Kacman62/Moonbeam-Synthesizer/CodeFolder/images.cpp

#include "images.h"

const unsigned char PKI_Logo_BW[] = {
    // 'PKIndustries_LowRes_BW', 128x64px
    0x00, 0x00, 0x00, 0x00, 0x00, 0x00, 0x00, 0x00, 0x00, 0x00, 0x00, 0x00, 0x00, 0x00, 0x00, 0x01,
    0x00, 0x00, 0x00, 0x00, 0x00, 0x00, 0x00, 0x00, 0x00, 0x00, 0x00, 0x00, 0x00, 0x00, 0x00, 0x01,
    0x00, 0x00, 0x00, 0x00, 0x00, 0x00, 0x00, 0x00, 0x00, 0x00, 0x00, 0x00, 0x00, 0x00, 0x00, 0x01,
    0x00, 0x00, 0x00, 0x00, 0x00, 0x00, 0x00, 0x00, 0x00, 0x00, 0x00, 0x00, 0x00, 0x00, 0x00, 0x01,
    0x00, 0x00, 0x00, 0x00, 0x00, 0x00, 0x00, 0x00, 0x00, 0x00, 0x00, 0x00, 0x00, 0x00, 0x00, 0x01,
    0x00, 0x00, 0x00, 0x00, 0x00, 0x00, 0x00, 0x00, 0x00, 0x00, 0x00, 0x00, 0x00, 0x00, 0x00, 0x01,
    0x00, 0x00, 0x00, 0x00, 0x00, 0x00, 0x00, 0x00, 0x00, 0x00, 0x00, 0x00, 0x20, 0x00, 0x00, 0x01,
    0x00, 0x00, 0x00, 0x00, 0x00, 0x00, 0x00, 0x00, 0x00, 0x00, 0x00, 0x00, 0x20, 0x00, 0x00, 0x01,
    0x00, 0x00, 0x00, 0x00, 0x00, 0x00, 0x00, 0x00, 0x00, 0x00, 0x00, 0x00, 0x20, 0x00, 0x00, 0x01,
    0x00, 0x00, 0x00, 0x00, 0x00, 0x00, 0x00, 0x00, 0x00, 0x00, 0x00, 0x00, 0x20, 0x00, 0x00, 0x01,
    0x00, 0x00, 0x00, 0x00, 0x00, 0x00, 0x00, 0x00, 0x00, 0x00, 0x00, 0x00, 0x20, 0x00, 0x00, 0x01,
    0x00, 0x00, 0x00, 0x00, 0x00, 0x00, 0x00, 0x00, 0x00, 0x00, 0x00, 0x00, 0x20, 0x00, 0x00, 0x01,
    0x00, 0x00, 0x00, 0x00, 0x00, 0x00, 0x00, 0x00, 0x00, 0x00, 0x00, 0x00, 0x20, 0x00, 0x00, 0x01,
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

const unsigned char *notes[7] = {
    A, B, C, D, E, F, G};

// 'MoonBeamSynthExport', 8x8px
const unsigned char sharp[] = {
    0x00, 0x28, 0x7c, 0x28, 0x7c, 0x28, 0x00, 0x00};
// 'MoonBeamSynthExport', 8x8px
const unsigned char flat[] = {
    0x00, 0x40, 0x40, 0x70, 0x50, 0x70, 0x00, 0x00};

// 'MoonBeamSynthExport', 3x5px
const unsigned char one[] = {
    0x20, 0x20, 0x20, 0x20, 0x20};
// 'MoonBeamSynthExport', 3x5px
const unsigned char two[] = {
    0xc0, 0x20, 0x40, 0x80, 0xe0};
// 'MoonBeamSynthExport', 3x5px
const unsigned char three[] = {
    0xe0, 0x20, 0xe0, 0x20, 0xe0};
// 'MoonBeamSynthExport', 3x5px
const unsigned char four[] = {
    0xa0, 0xa0, 0xe0, 0x20, 0x20};
// 'MoonBeamSynthExport', 3x5px
const unsigned char five[] = {
    0xe0, 0x80, 0x40, 0x20, 0xc0};
// 'MoonBeamSynthExport', 3x5px
const unsigned char six[] = {
    0xe0, 0x80, 0xe0, 0xa0, 0xe0};
// 'MoonBeamSynthExport', 3x5px
const unsigned char seven[] = {
    0xe0, 0x20, 0x40, 0x40, 0x40};
// 'MoonBeamSynthExport', 3x5px
const unsigned char eight[] = {
    0xe0, 0xa0, 0xe0, 0xa0, 0xe0};
// 'MoonBeamSynthExport', 3x5px
const unsigned char nine[] = {
    0xe0, 0xa0, 0xe0, 0x20, 0xe0};
// 'MoonBeamSynthExport', 3x5px
const unsigned char zero[] = {
    0xe0, 0xa0, 0xa0, 0xa0, 0xe0};

// Array of all bitmaps for convenience. (Total bytes used to store images in PROGMEM = 160)

const unsigned char *numbers[10] = {
    zero, one, two, three, four, five, six, seven, eight, nine};

// 'MoonBeamSynthExport', 3x5px
const unsigned char plus[] = {
    0x00, 0x40, 0xe0, 0x40, 0x00};
// 'MoonBeamSynthExport', 3x5px
const unsigned char minus[] = {
    0x00, 0x00, 0xe0, 0x00, 0x00};
