Kacman62/Moonbeam-Synthesizer/CodeFolder/images.h

#ifndef IMAGES_H
#define IMAGES_H

extern const unsigned char PKI_Logo_BW[];

extern const unsigned char MoonBeamSynth[];

extern const unsigned char sinWave[];
extern const unsigned char triWave[];
extern const unsigned char sawWave[];
extern const unsigned char squareWave[];
extern const unsigned char *waveTable[];

extern const unsigned char slider[];

extern const unsigned char menuHeader[];

extern const unsigned char diagnosticsMenu[];
extern const unsigned char mainMenu[];
extern const unsigned char OSCMenu[];
extern const unsigned char ADSRMenu[];
extern const unsigned char waveFormMenu[];
extern const unsigned char settingsMenu[];

extern const unsigned char *menuItems[];
extern const int menuItemsNum;

extern const unsigned char *notes[];
extern const unsigned char *numbers[];

extern const unsigned char sharp[];
extern const unsigned char flat[];

extern const unsigned char plus[];
extern const unsigned char minus[];

#endif
